usetraces/traces/demo/demo.kicad_sch

## KiCad design demo/demo.kicad_sch (2026-06-25)

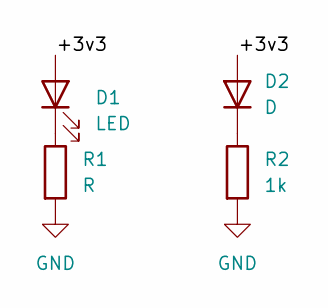
[picture p3: schematic demo.kicad_sch]

Parts:
D1: LED; D_0402_1005Metric_Pad0.77x0.64mm_HandSolder; LCSC C71911
D2: D; D_0402_1005Metric_Pad0.77x0.64mm_HandSolder; LCSC C74339
R1: R; R_0402_1005Metric_Pad0.72x0.64mm_HandSolder; Digikey Part Number 311-1.00KLRTR-ND
R2: 1k; R_0402_1005Metric_Pad0.72x0.64mm_HandSolder; Mouser Part Number 71-CRCW0402-1.0K-E3

Connections:
+3v3: D1.2 (A), D2.2 (A)
GND: R1.2, R2.2
unnamed: D1.1 (K), R1.1
unnamed: D2.1 (K), R2.1
